mausi-mick/KSE/KS-Current-Source.drawio.pdf

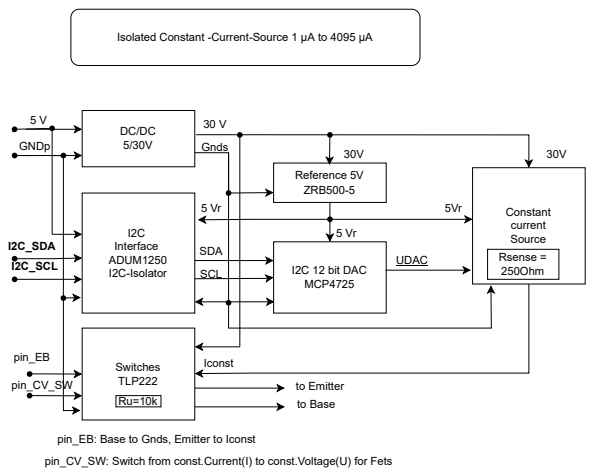
[picture p8: page 1]
I2C Interface ADUM1250 I2C-Isolator; Constant current Source; Switches TLP222; Reference 5V ZRB500-5; I2C 12 bit DAC MCP4725; SDA; SCL; GNDp; I2C_SDA; I2C_SCL; 30V Gnds; UDAC; Iconst; to Emitter to Base; pin_EB; pin_CV_SW; Rsense = 250Ohm

Isolated Constant -Current-Source 1 µA to 4095 µA

pin_EB: Base to Gnds, Emitter to Iconst
pin_CV_SW: Switch from const.Current(I) to const.Voltage(U) for Fets
