mausi-mick/KSE/CCS_I2C_7.pdf

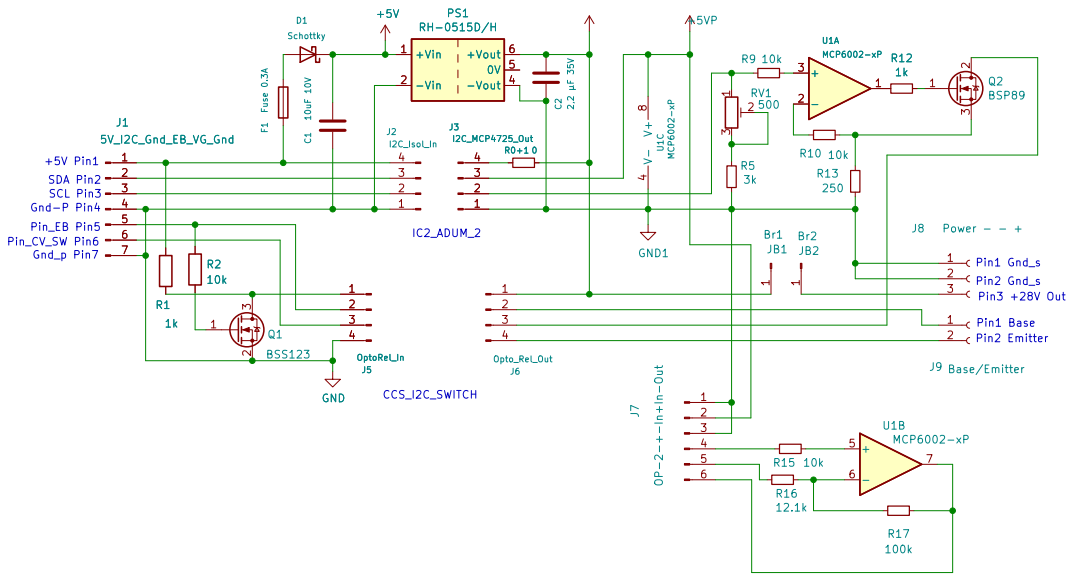
[picture p13: page 1]
