mausi-mick/KSE/CCS_Base_0.pdf

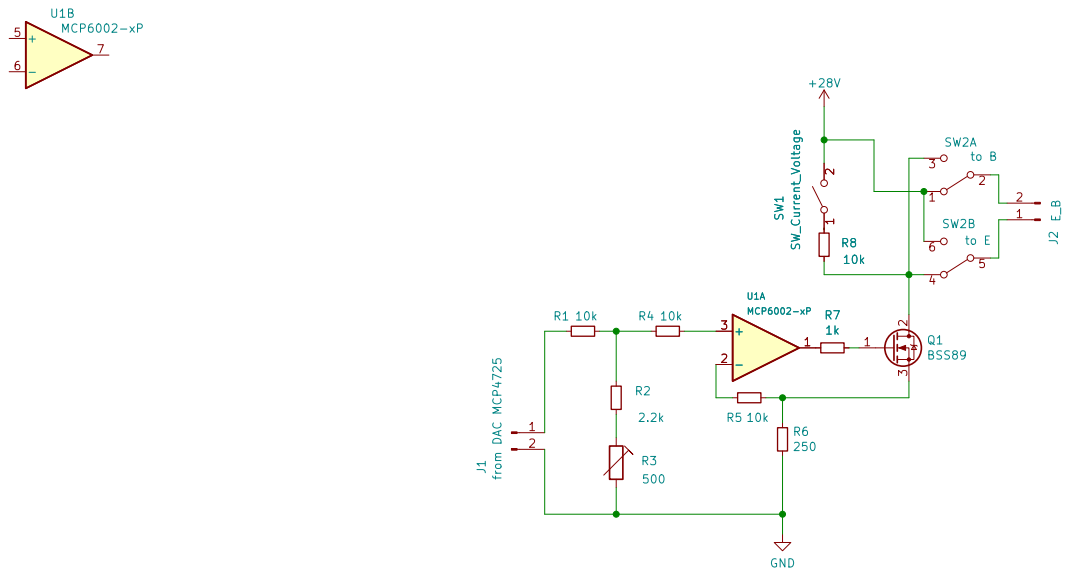
[picture p14: page 1]
